Nauman3S/SmartTControl/artwork/buck.jpg

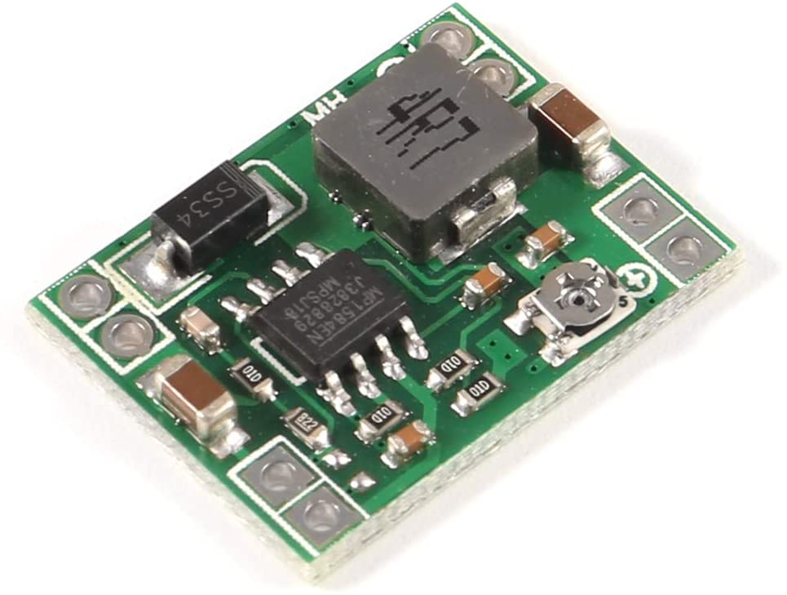
artwork/buck.jpg
