Nauman3S/SmartTControl/artwork/CompArch.png

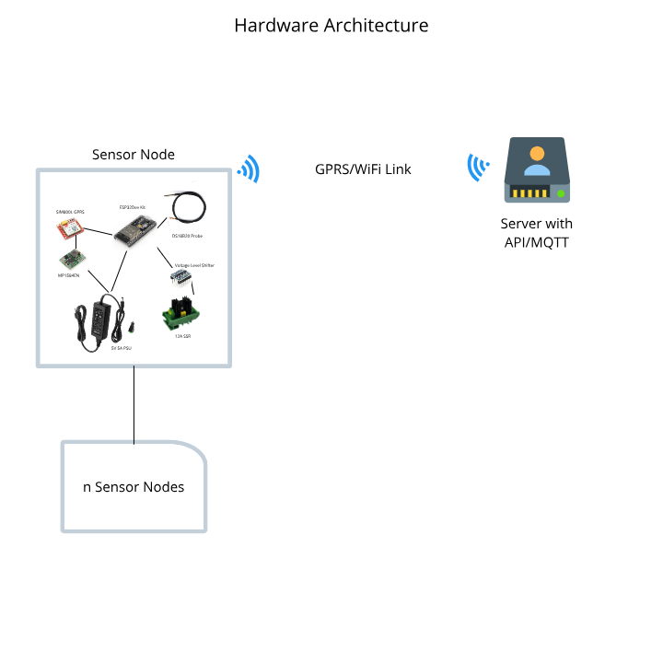
artwork/CompArch.png
