Nauman3S/SmartTControl/artwork/esp32.jpg

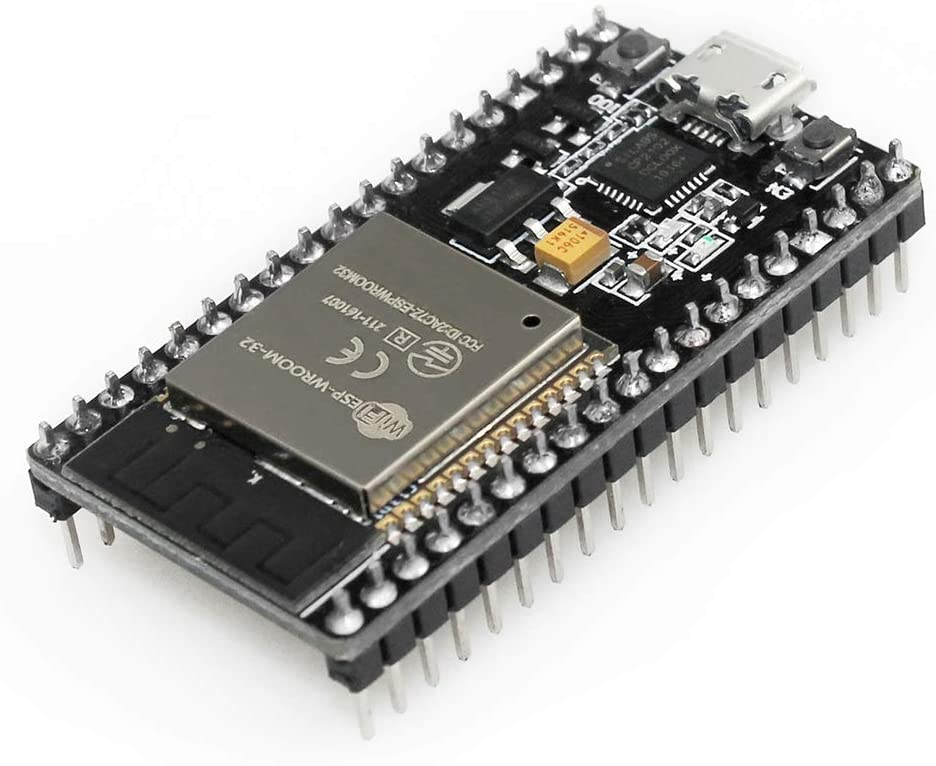
artwork/esp32.jpg
