Nauman3S/SmartTControl/artwork/sim800l.jpg

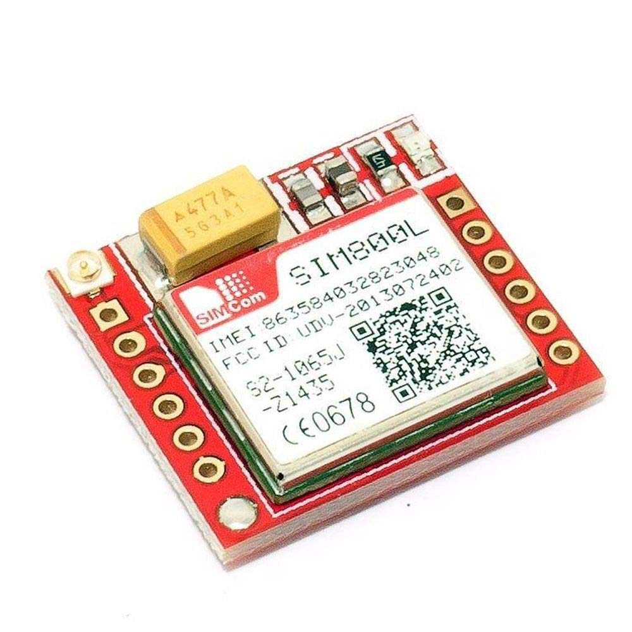
artwork/sim800l.jpg
