Nauman3S/SmartTControl/PCB/PCB_PCB_RemoteTController_2021-05-22.pdf

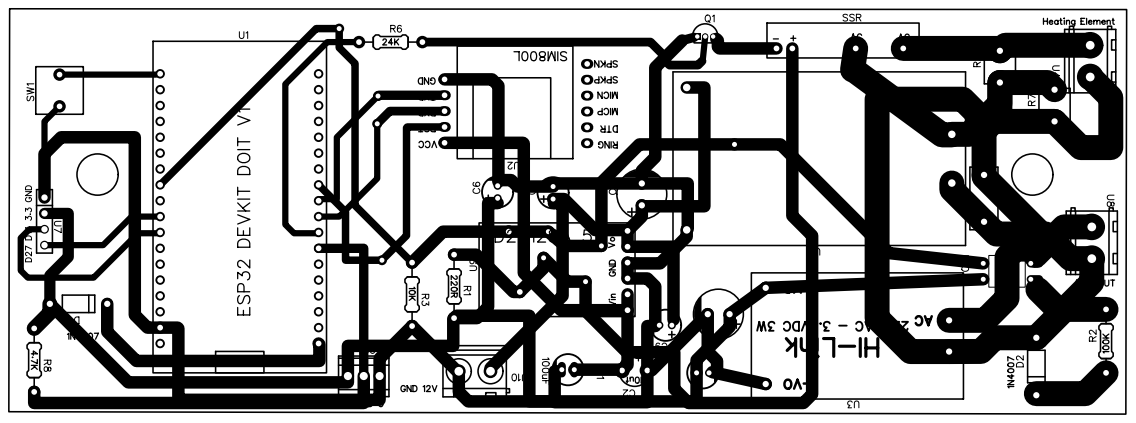
[picture p27: page 1]
