Nauman3S/SmartTControl/PCB/PCB_PCB_RemoteTController_2021-05-17.pdf

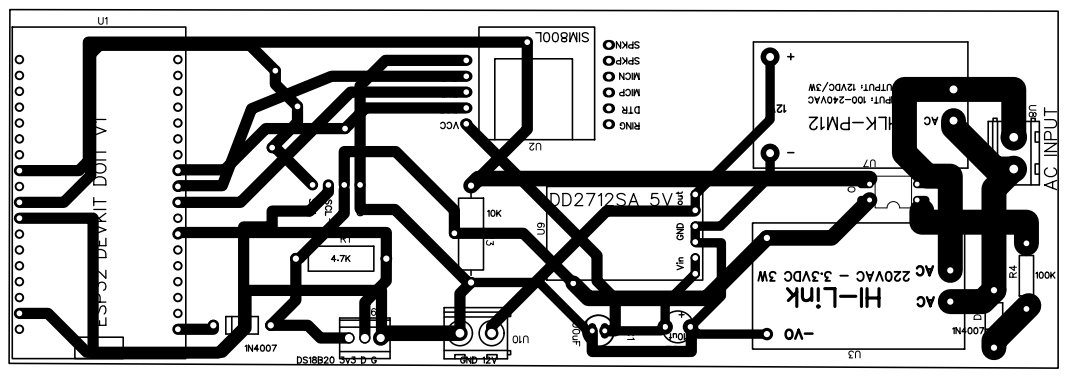
[picture p28: page 1]
