Nauman3S/SmartTControl/PCB/PCB_PCB_RemoteTController_2021-05-25(1).pdf

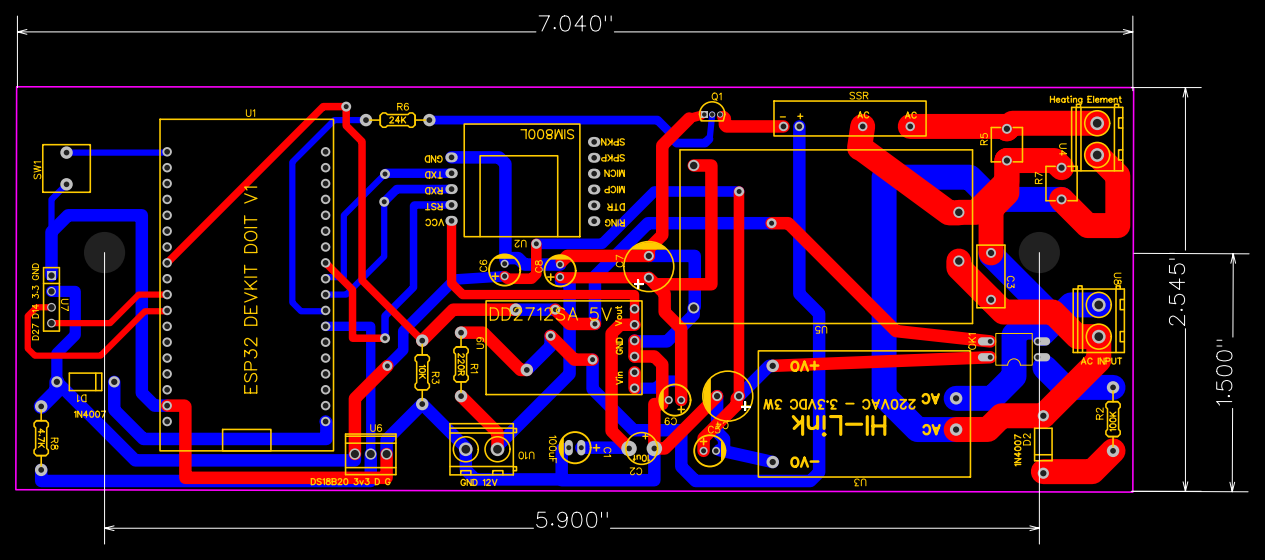
[picture p29: page 1]
