Nauman3S/SmartTControl/PCB/PCB_PCB_RemoteTController_2021-05-17(1).pdf

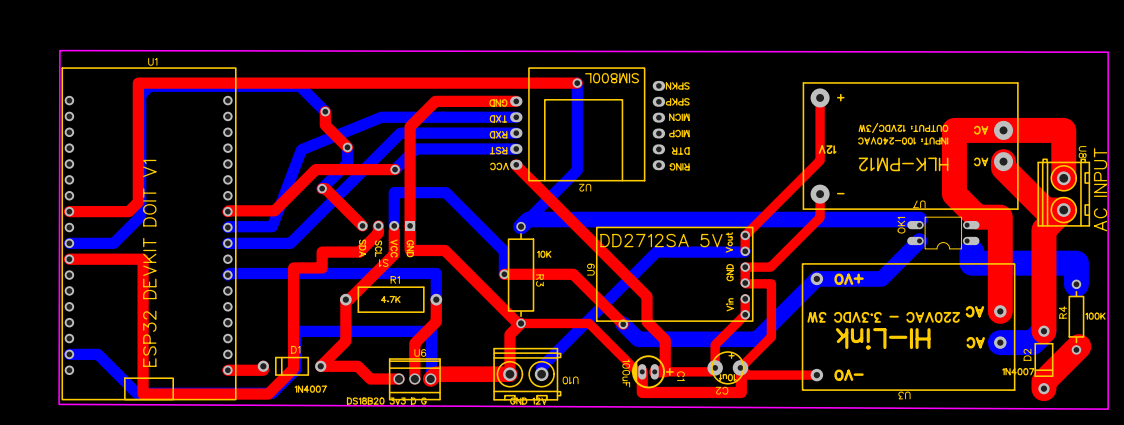
[picture p30: page 1]
